propane-and-electrons/tipsensor/hardware/tipsensor.sch

## KiCad design hardware/tipsensor.sch (2013-12-12)

Schematic: tipsensor.sch

Parts:
C1, C2: 1uF; C2
C3, C4, C5, C6, C7: 0.1uF; C2
D1: 1N4004; D3
D2: 1N400x; D3
D3: SOLOUT; LED-3MM
D4: SOLPWR; LED-3MM
D5: LED; LED-3MM
H1, H2, H3, H4: SCREWHOLE; 1pin
P1: SOLOUT; PP-2H-5MMSCREWTERM
P2: POWER; PP-2H-5MMSCREWTERM
P3: SOLPWR; PP-2H-5MMSCREWTERM
P4: SFE_BREAKOUT; SIL-6
P5: CONN_3X2; ICSP_3X2
Q1: IRF510; TO220GDS_VERT
R1: 390; R3
R2, R6: 10k; R3
R3, R4: 1k; R3
R5: 100R; R3
SW1: POWER; SIL-3
SW2: SW_PUSH; SW-6MM-4PIN
U1: 4N35; DIP-6__300
U2: MCP1700; SIL-3
U3: ADXL335; LFCSP_LQ_16
U4: ATTINY84-P; DIP-14__300
